You-Telecom-Provedor-de-internet/YouSimuladorOBD/assets/validation/phone_screen.jpg

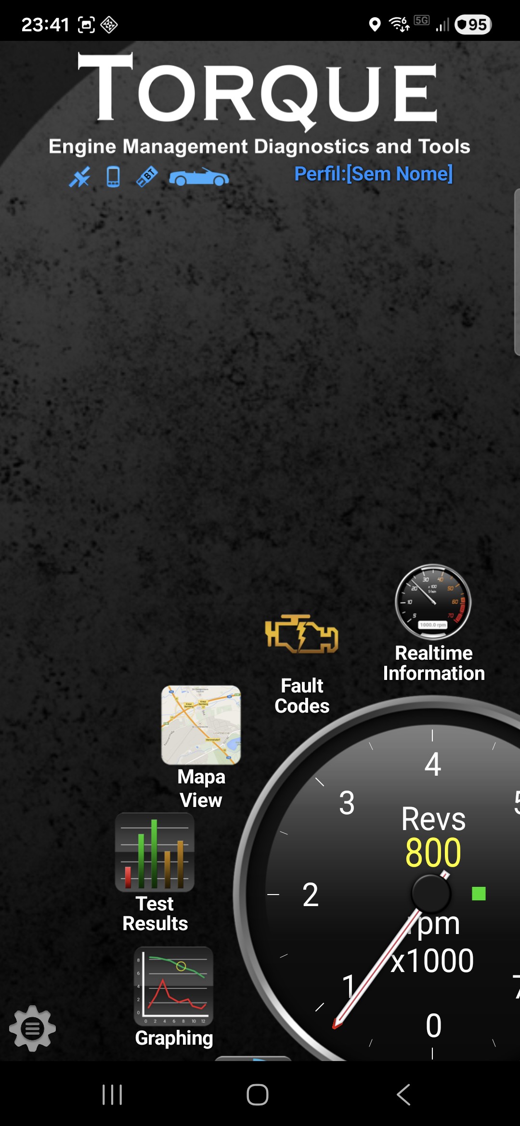
assets/validation/phone_screen.jpg
